fjaderboll/peekaboo/body-parts/addon_bar_test.scad

bw = 80;  // base width
wt = 2;   // wall thickness

use <addon_support.scad>

addon_bar(bw-2*wt);
